evanofslack/macropad/Images/BlackBackground.JPG

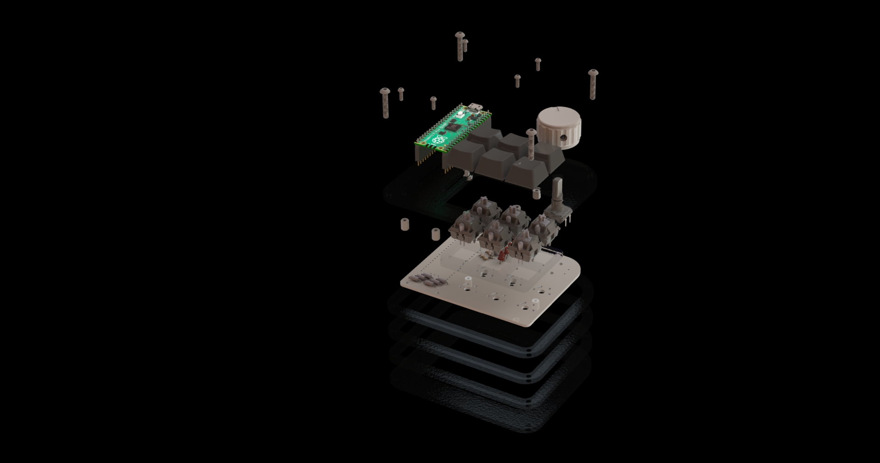
Images/BlackBackground.JPG
