evanofslack/macropad/Images/Render_v3.PNG

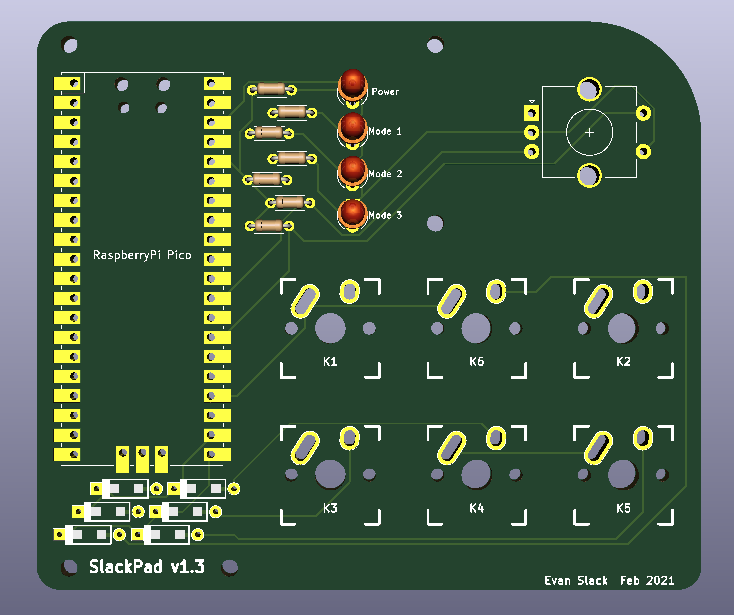
Images/Render_v3.PNG
