evanofslack/macropad/Images/SlackPadv1.3 Render 2.JPG

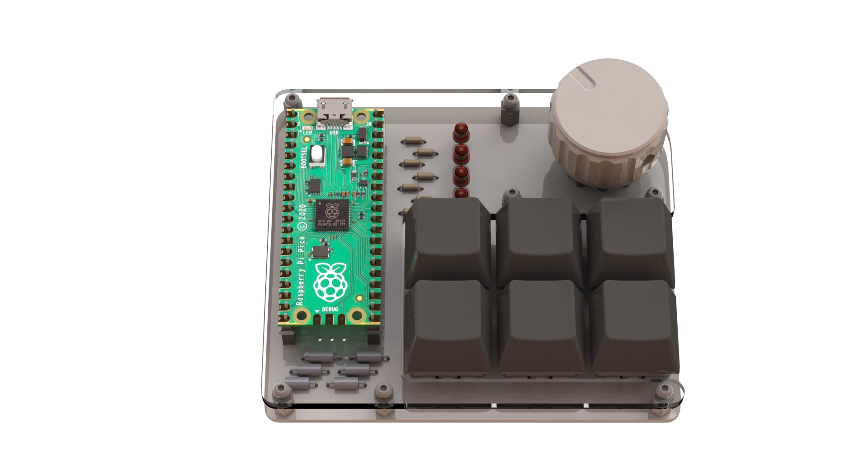
Images/SlackPadv1.3 Render 2.JPG
