evanofslack/macropad/CAD/02_OTS/92095A184_BUTTON HEAD HEX DRIVE SCREW.SLDPRT

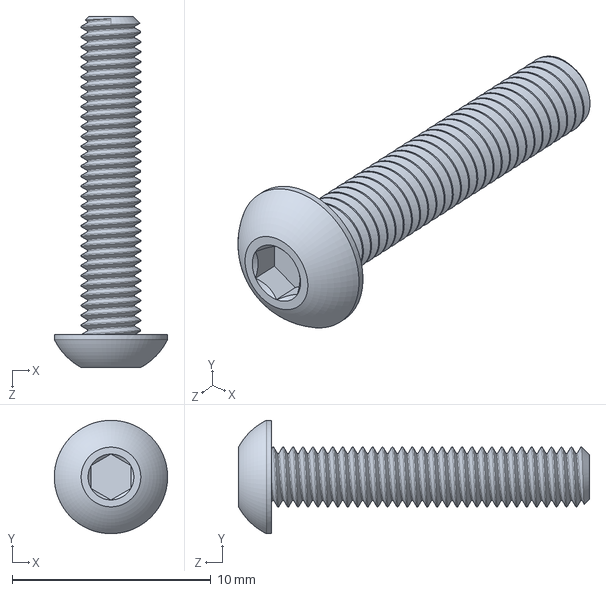
[picture p24: CAD file, 2021-03-28]
CAD/02_OTS/92095A184_BUTTON HEAD HEX DRIVE SCREW.SLDPRT
5.70 x 5.70 x 17.7 mm
